fabi1cazenave/Quacken/output/pcbs/back.png

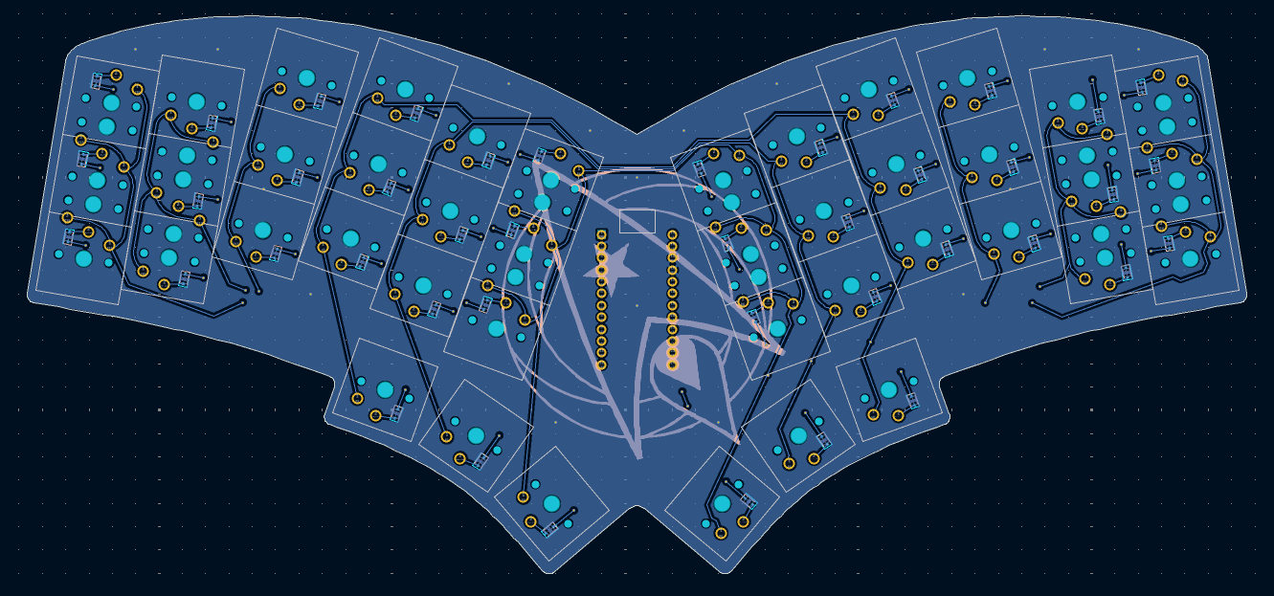
output/pcbs/back.png
