fabi1cazenave/Quacken/output/pcbs/front.png

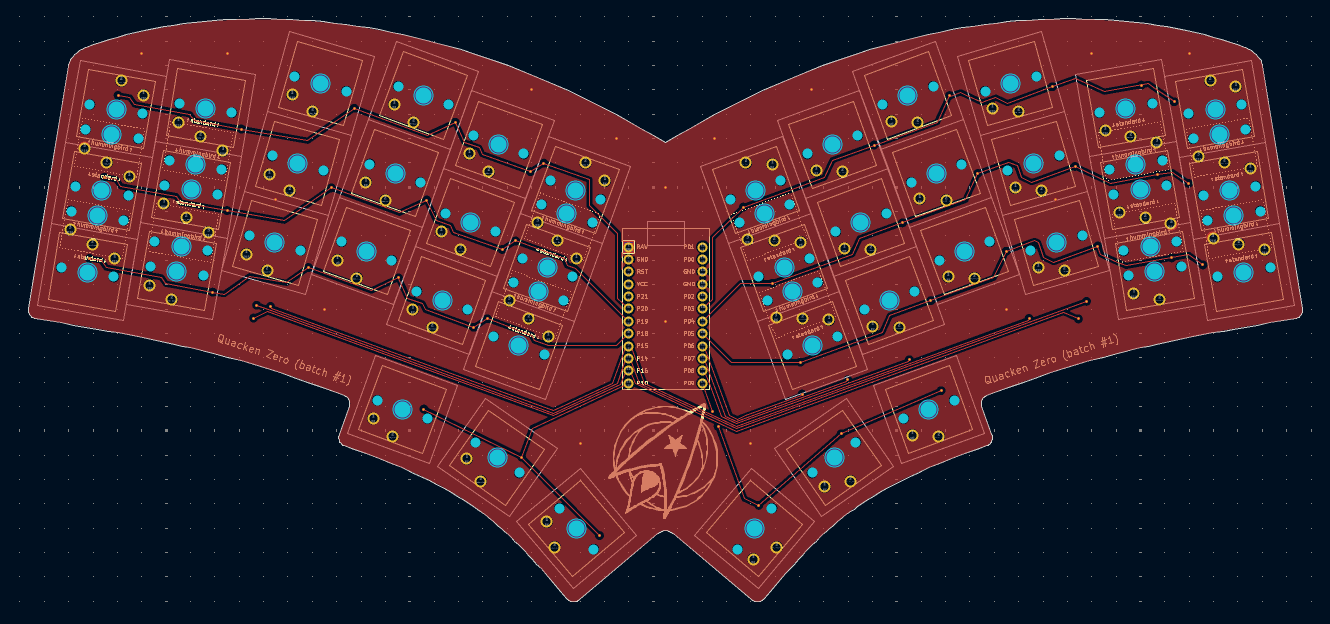
output/pcbs/front.png
